scortua/IDIE_PROJECT/Documentos/Recapitulacion/Box.pdf

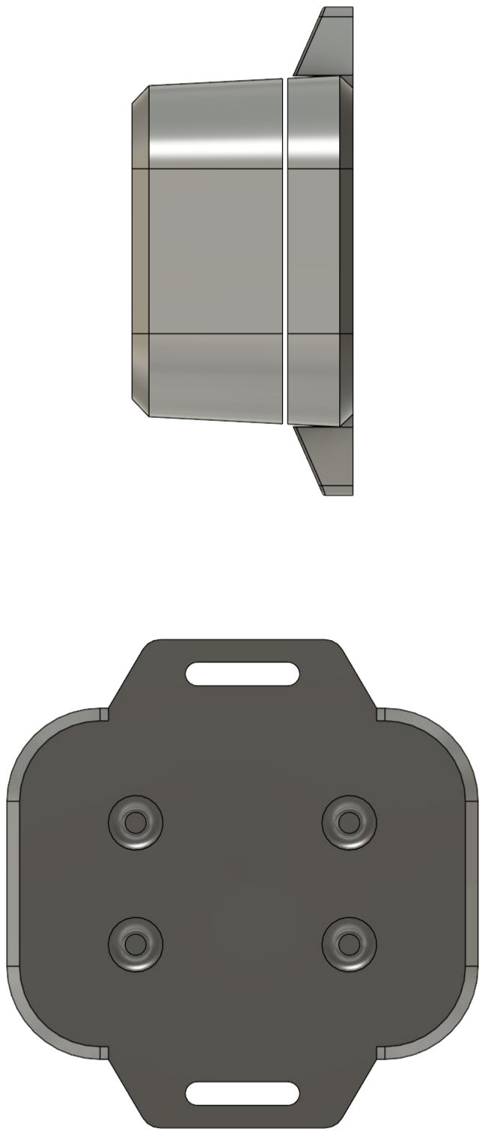
[picture p6: figure]

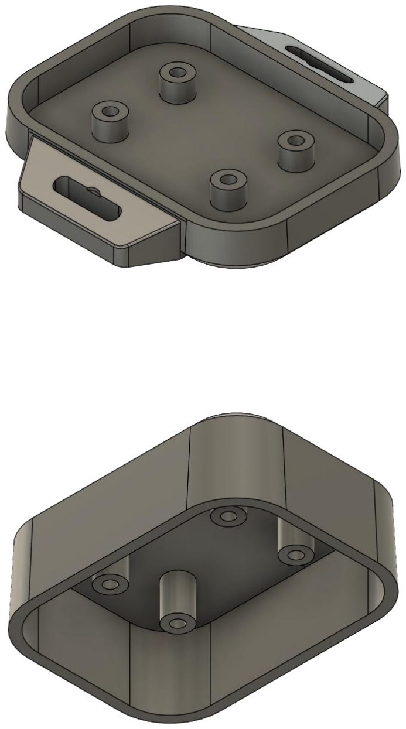
[picture p7: figure]

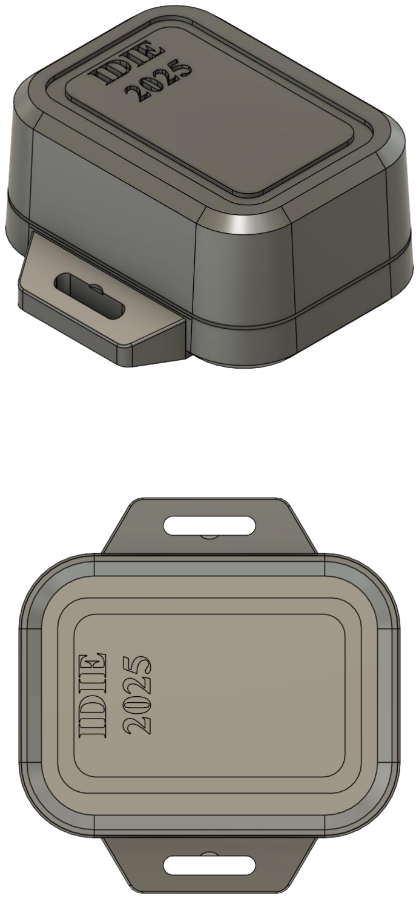
[picture p8: figure]
