scortua/IDIE_PROJECT/Documentos/Recapitulacion/PCB.pdf

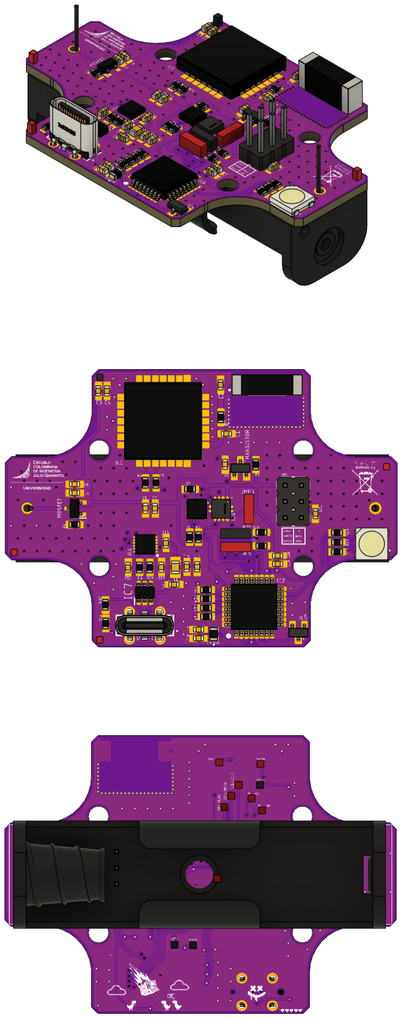
[picture p9: page 1]
